TheFaceCo/Subaru-ABS-converter/Docs/2015-04-21 12.51.15.jpg

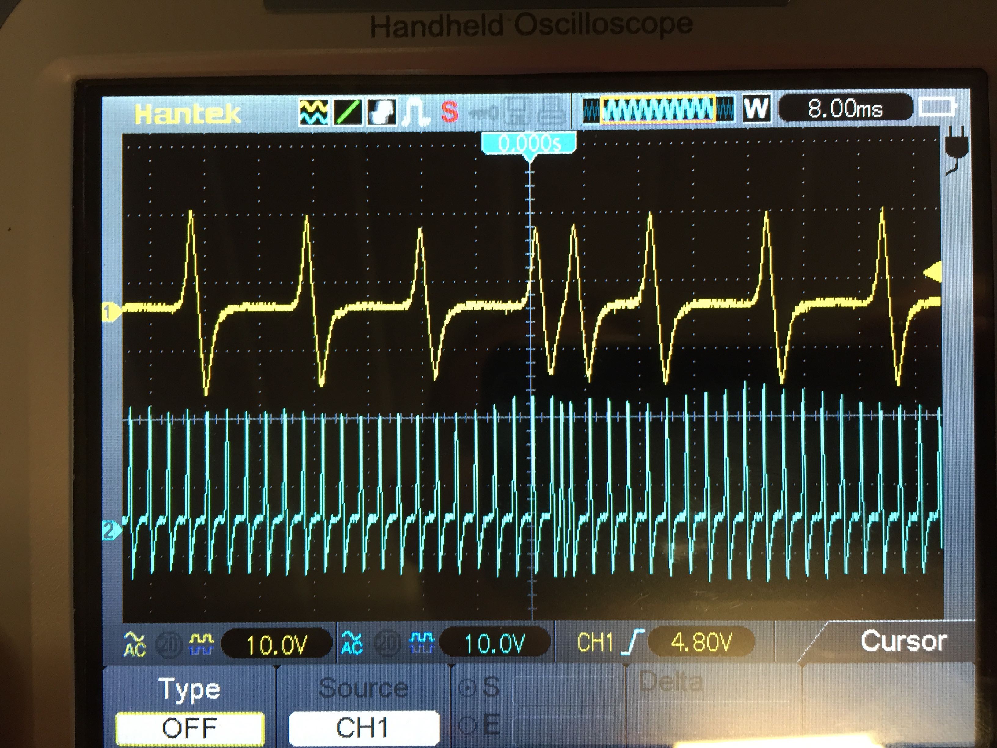
Docs/2015-04-21 12.51.15.jpg
