TheFaceCo/Subaru-ABS-converter/Docs/ABS converter board top.png

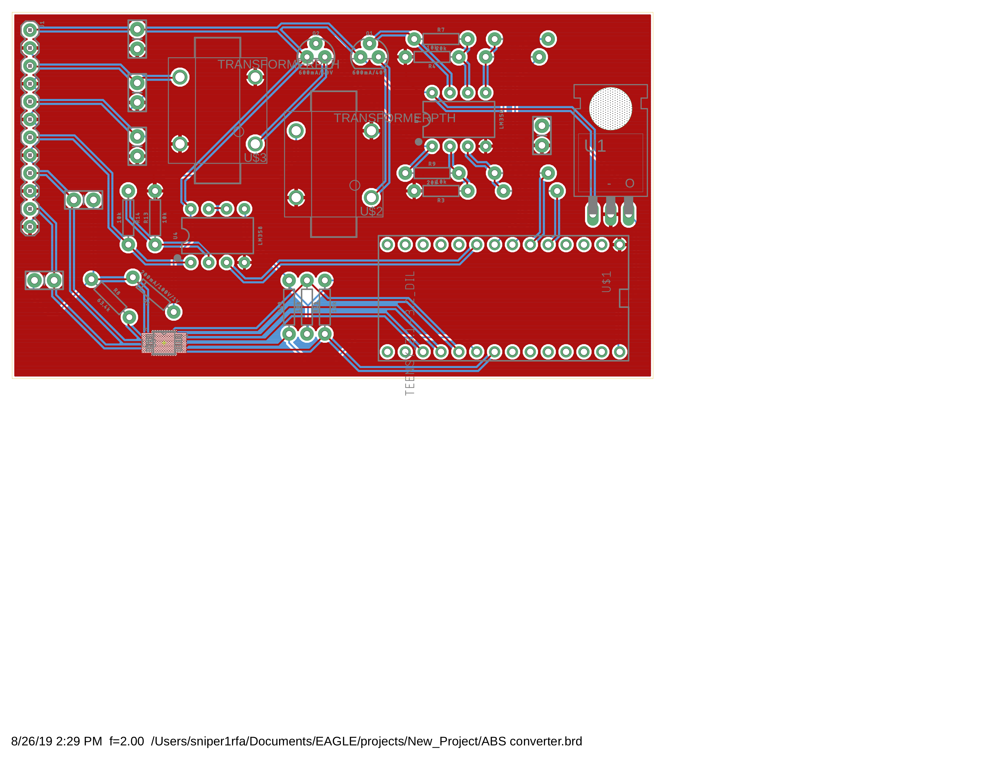
Docs/ABS converter board top.png
