TheFaceCo/Subaru-ABS-converter/Docs/ABS converter board.png

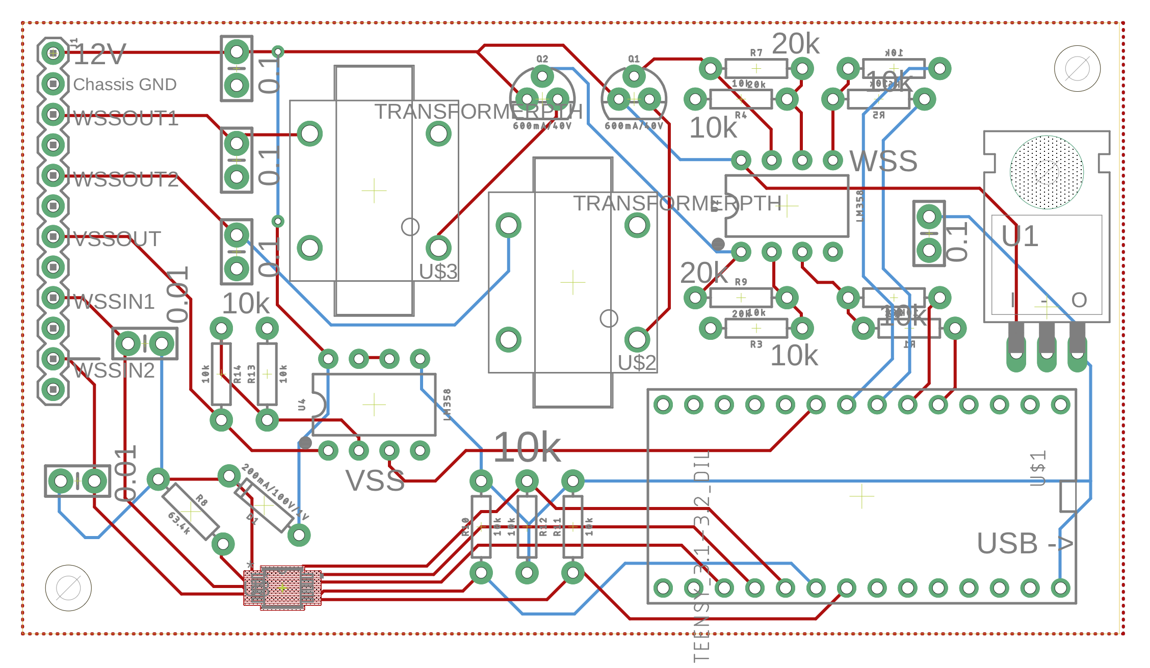
Docs/ABS converter board.png
