TheFaceCo/Subaru-ABS-converter/Docs/ABS converter.png

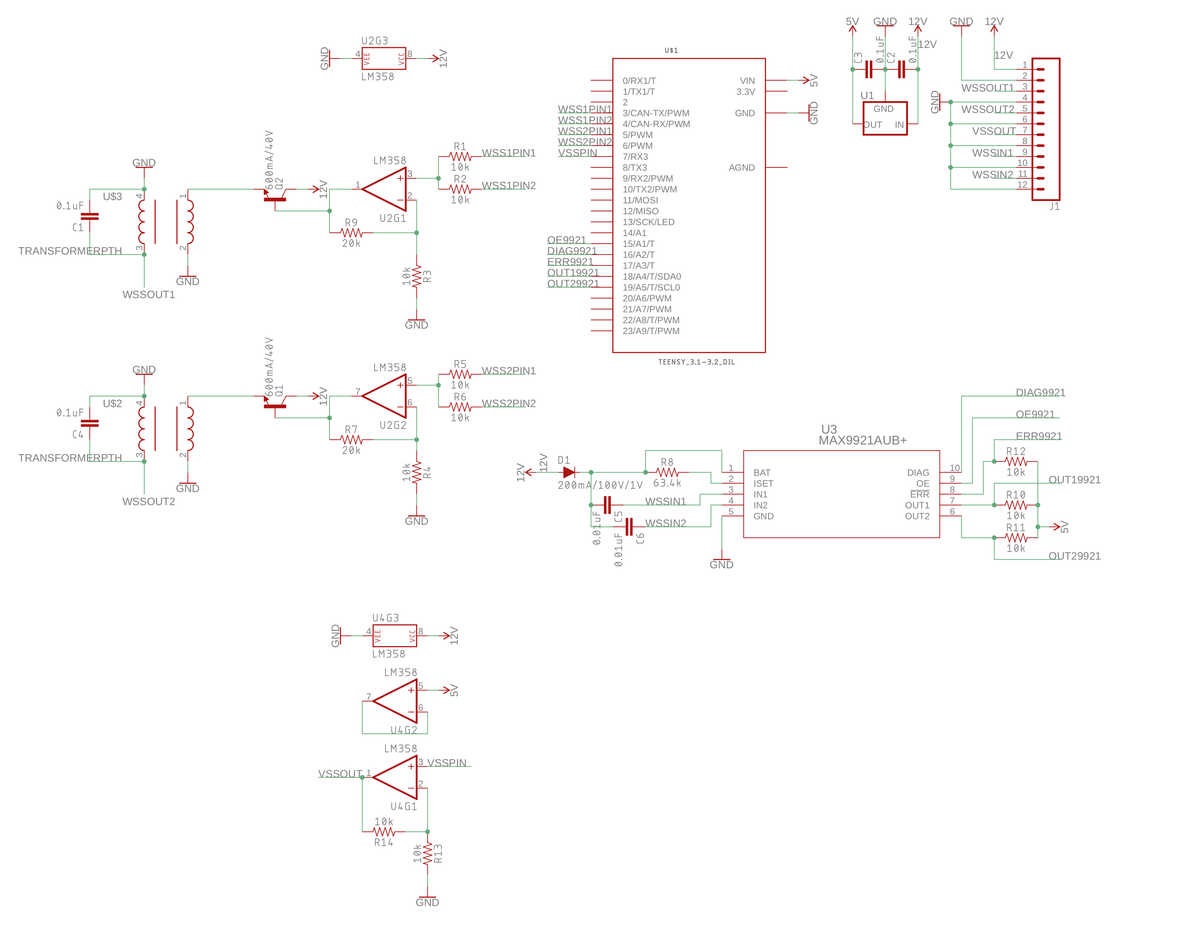
Docs/ABS converter.png
