TheFaceCo/Subaru-ABS-converter/Docs/aef66e297d76e45f90afa9533d9f82be.png

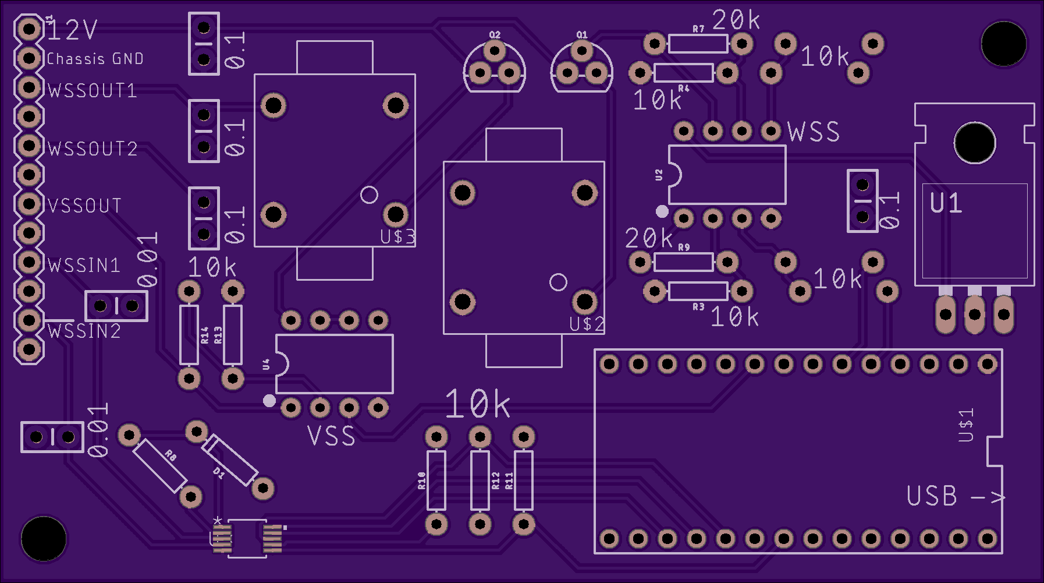
Docs/aef66e297d76e45f90afa9533d9f82be.png
