TheFaceCo/Subaru-ABS-converter/Docs/af2526ec700ece2c94f77b1ed76ad9c0.jpg

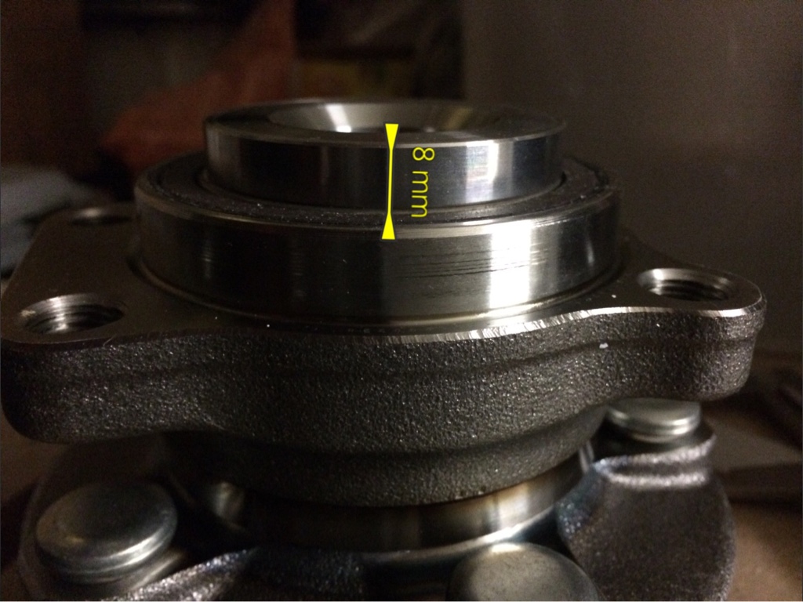
Docs/af2526ec700ece2c94f77b1ed76ad9c0.jpg
