TheFaceCo/Subaru-ABS-converter/Docs/DSC_1161.JPG

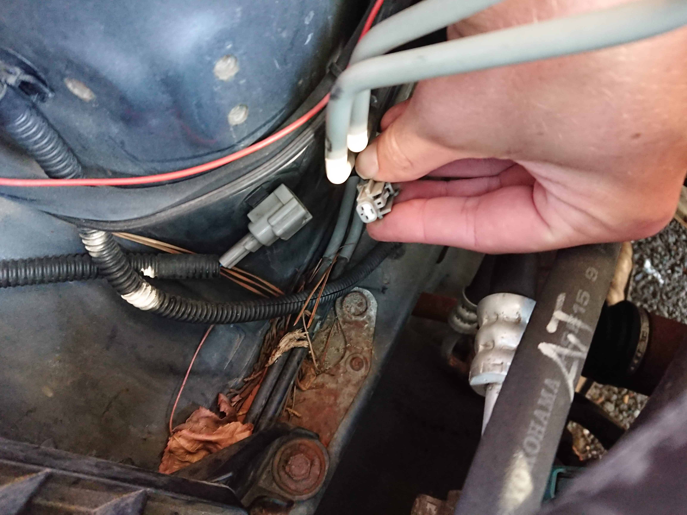
Docs/DSC_1161.JPG
