TheFaceCo/Subaru-ABS-converter/Docs/DSC_1220.JPG

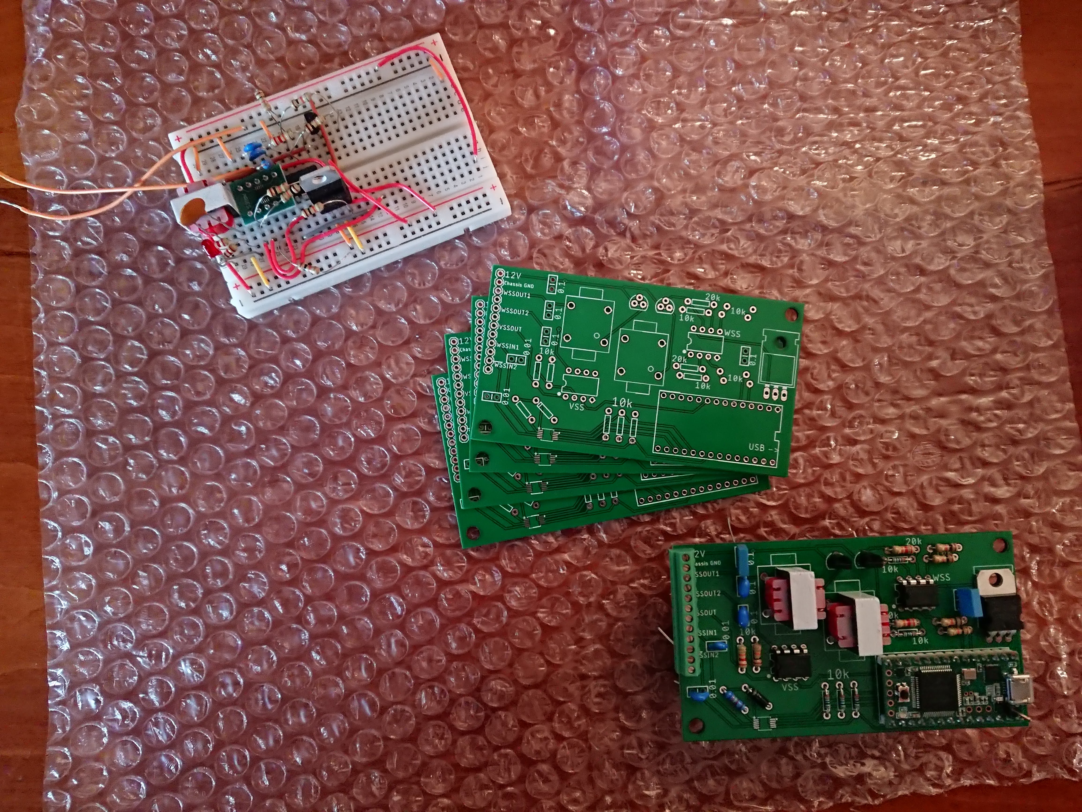
Docs/DSC_1220.JPG
