TheFaceCo/Subaru-ABS-converter/Docs/DSC_1224.JPG

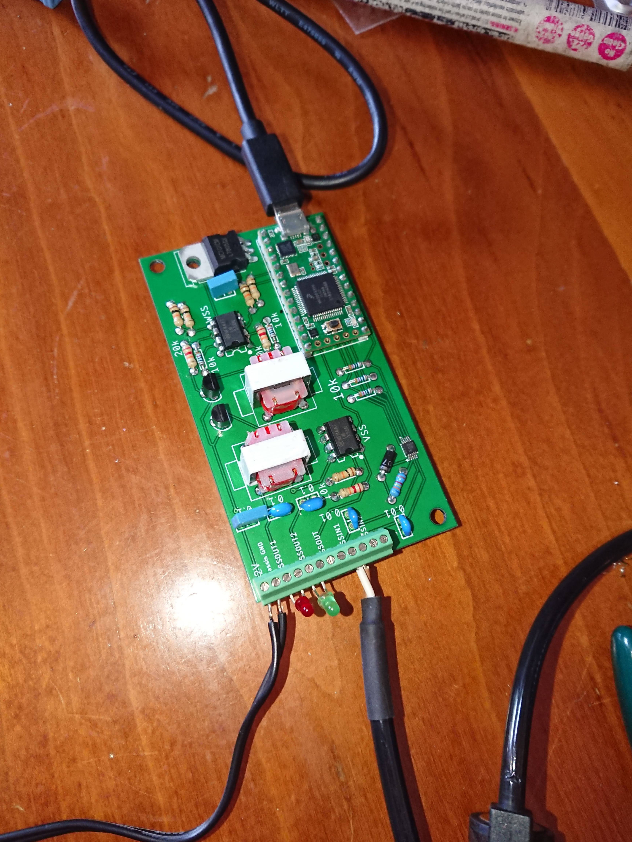
Docs/DSC_1224.JPG
