TheFaceCo/Subaru-ABS-converter/Docs/Magnetic tone ring.JPG

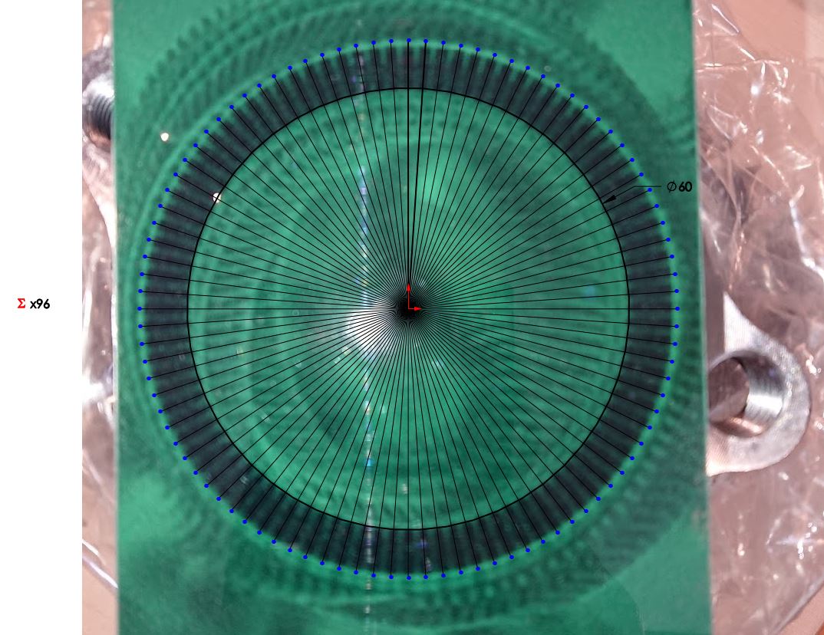
Docs/Magnetic tone ring.JPG
